kquinsland/hdmi-kvm-esphome/docs/from_seller/01.png

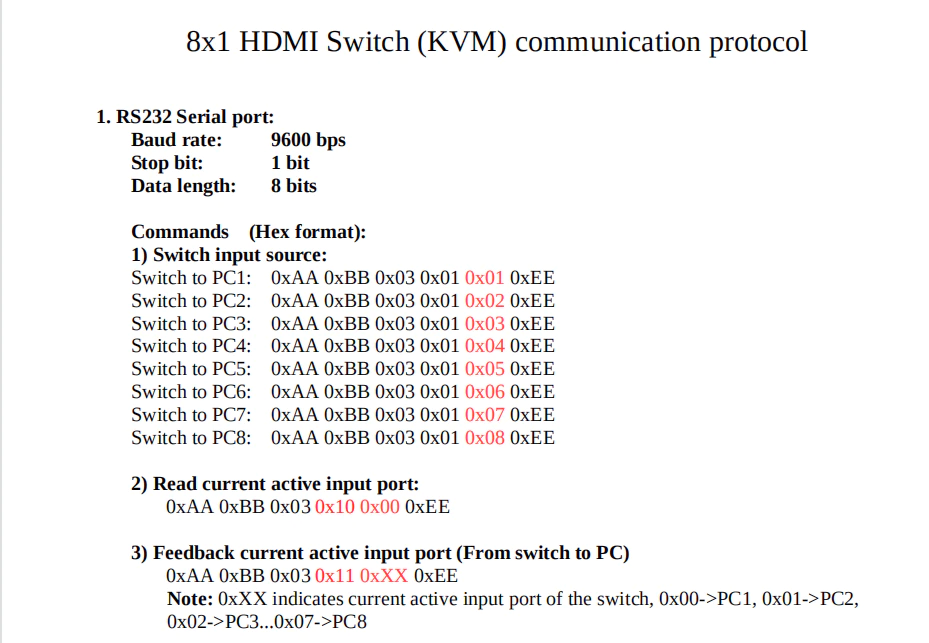
docs/from_seller/01.png
