kquinsland/hdmi-kvm-esphome/docs/from_seller/02.jpg

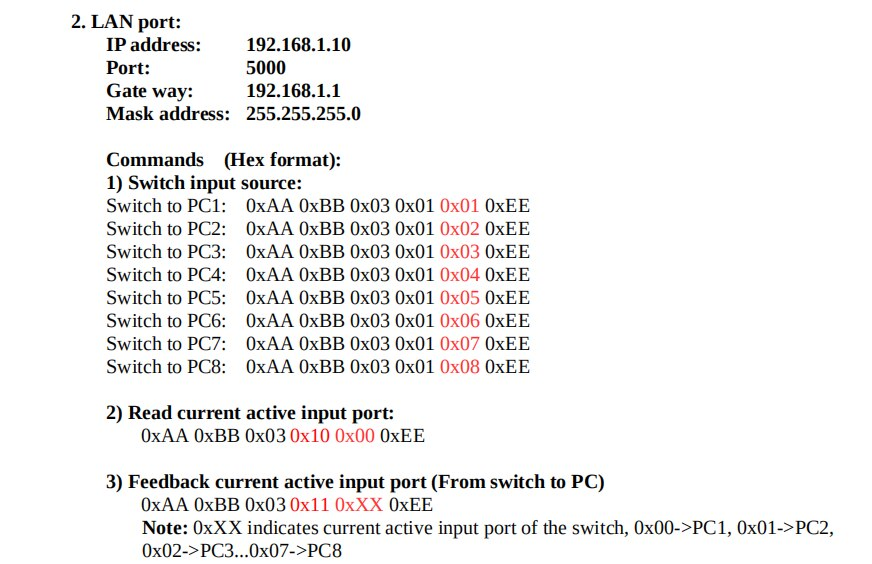
docs/from_seller/02.jpg
